Matesxs/ESP32FanController/Code/src/led_strips/effects/base_effect.h

#pragma once

#include <Arduino.h>

class LedState;

class BaseEffect
{  
public:
  LedState *state;
  unsigned long start;
  
  BaseEffect()
  {
    start = millis();
  }
  
  virtual void render() = 0;
};
