Matesxs/ESP32FanController/Code/src/led_strips/effects/solid_color.h

#pragma once

#include <NeoPixelBus.h>

#include "lerper.h"
#include "mic/utils.h"
#include "base_effect.h"
#include "led_strips/led_state.h"

class SolidColor: public BaseEffect
{
public:
  RgbColor rgb = {0, 0, 0};

  SolidColor()
  {
  }

  SolidColor(uint8_t *color)
  {
    for(int i = 0; i < 3; i++)
      rgb[i] = color[i];
  }
  
  virtual void render()
  {
    for(int i = 0; i < state->count; i++)
      state->setRgb(i, rgb);
  }
};

class TemperatureSolidColor: public SolidColor
{
public:
  TemperatureSolidColor(uint64_t temperature_source, float min_temp, float max_temp) :
    m_temperatureSource(temperature_source),
    m_minTemp(min_temp),
    m_maxTemp(max_temp),
    m_lerpProgress(0.0)
  {
    float temperature = temperatureFromSource(temperature_source);
    m_targetTemperature = temperature;
    rgb = RgbColor(HslColor(temperatureToHue(temperature), 1.0, 0.5));
    m_lerper.setReference(&m_lerpProgress);
  }

  float temperatureToHue(float temperature)
  {
    return map(temperature, m_minTemp, m_maxTemp, static_cast<float>(115.0 / 360.0), static_cast<float>(0.0 / 360.0));
  }

  virtual void render()
  {
    float temperature = temperatureFromSource(m_temperatureSource);
    if (m_targetTemperature != temperature)
    {
      m_targetColor = RgbColor(HslColor(temperatureToHue(temperature), 1.0, 0.5));
      m_lerper.set(1.0, 500, 0.0);
      m_targetTemperature = temperature;
    }

    if (!m_lerper.finished())
    {
      m_lerper.update();
      SolidColor::rgb = RgbColor::LinearBlend(rgb, m_targetColor, static_cast<uint8_t>(m_lerpProgress * 255));
    }
    
    SolidColor::render();
  }

private:
  Lerper<float> m_lerper;
  float m_lerpProgress;
  float m_minTemp;
  float m_maxTemp;
  uint64_t m_temperatureSource;
  float m_targetTemperature;
  RgbColor m_targetColor = {0, 0, 0};
};
